ZimengXiong/ScrapNC/STLs/Z Assembly/M3 Spacer.stl

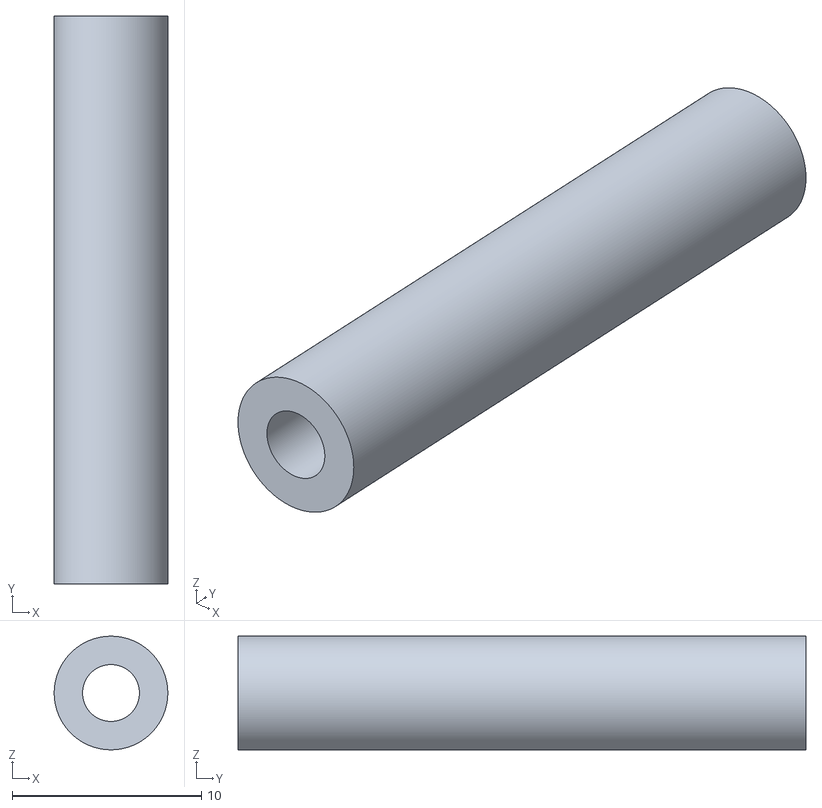
[picture p30: CAD file, 2025-07-05]
STLs/Z Assembly/M3 Spacer.stl
6.00 x 30.0 x 6.00
