ZimengXiong/ScrapNC/STLs/Electronics/Fly Pi Lite v2_DIN.stl

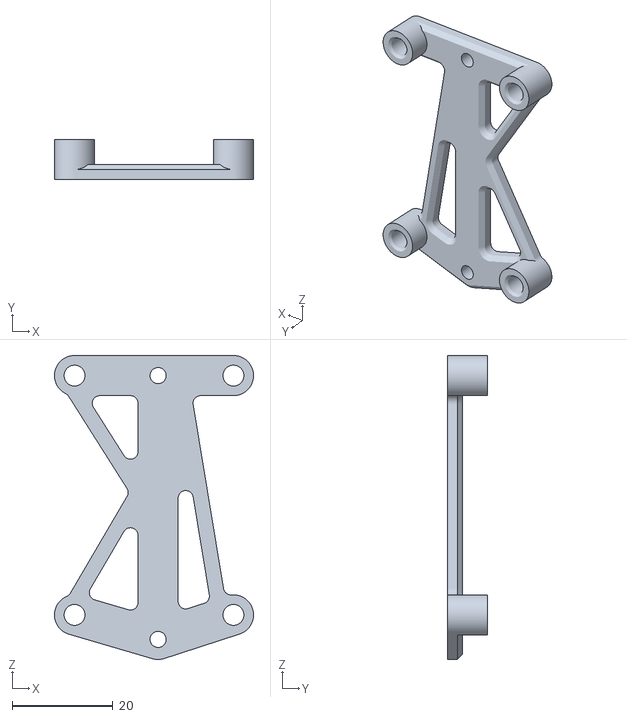
[picture p31: CAD file, 2025-07-05]
STLs/Electronics/Fly Pi Lite v2_DIN.stl
39.6 x 8.00 x 60.5
