ZimengXiong/ScrapNC/STLs/Y Axis Plate/Y Axis Plate Motor Mount.stl

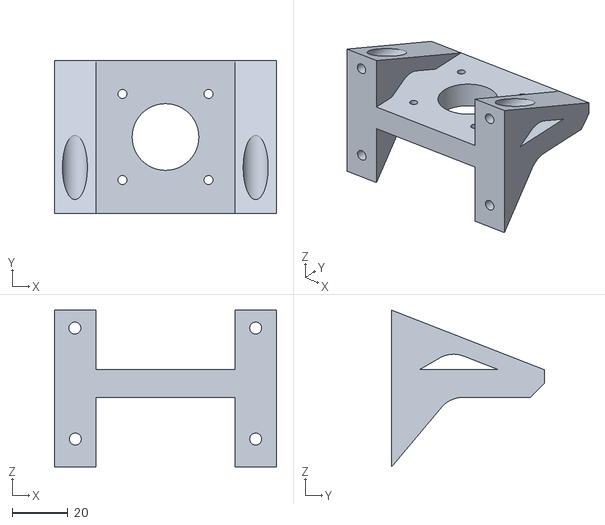
[picture p32: CAD file, 2025-07-05]
STLs/Y Axis Plate/Y Axis Plate Motor Mount.stl
80.0 x 55.0 x 56.4
