ZimengXiong/ScrapNC/STLs/Y Axis/Back Idler Mount Top.stl

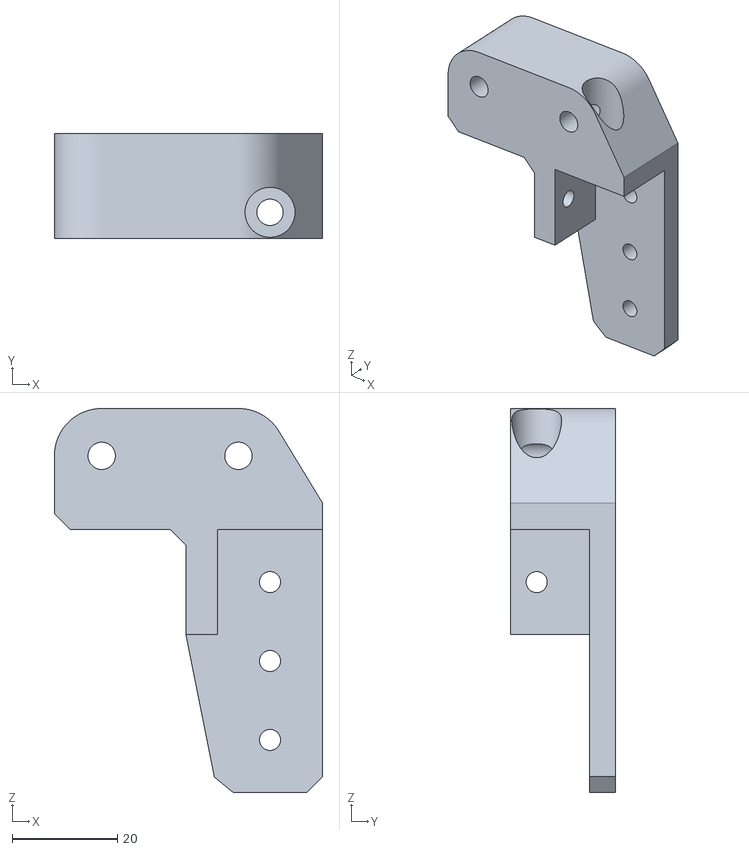
[picture p33: CAD file, 2025-07-05]
STLs/Y Axis/Back Idler Mount Top.stl
51.0 x 20.0 x 73.0
