ZimengXiong/ScrapNC/STLs/Y Axis Plate/Y Axis Belt Tensioner Module.stl

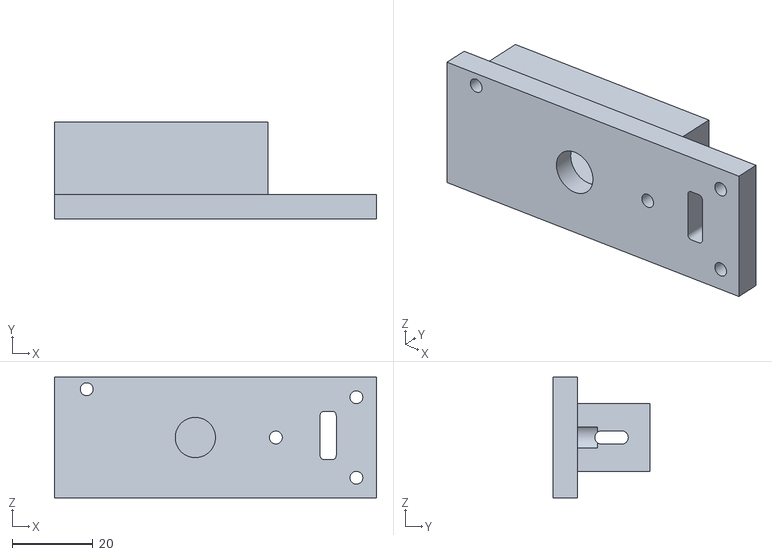
[picture p34: CAD file, 2025-07-05]
STLs/Y Axis Plate/Y Axis Belt Tensioner Module.stl
80.0 x 24.0 x 30.0
