ZimengXiong/ScrapNC/STLs/Y Axis/Back Idler Mount Bottom.stl

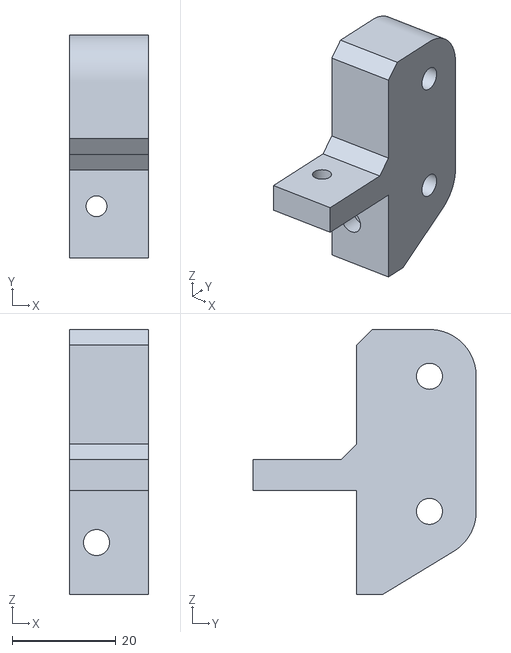
[picture p35: CAD file, 2025-07-05]
STLs/Y Axis/Back Idler Mount Bottom.stl
15.2 x 43.0 x 51.0
