ZimengXiong/ScrapNC/STLs/Y Axis Plate/Y Axis Plate Idler Tensioner Mount.stl

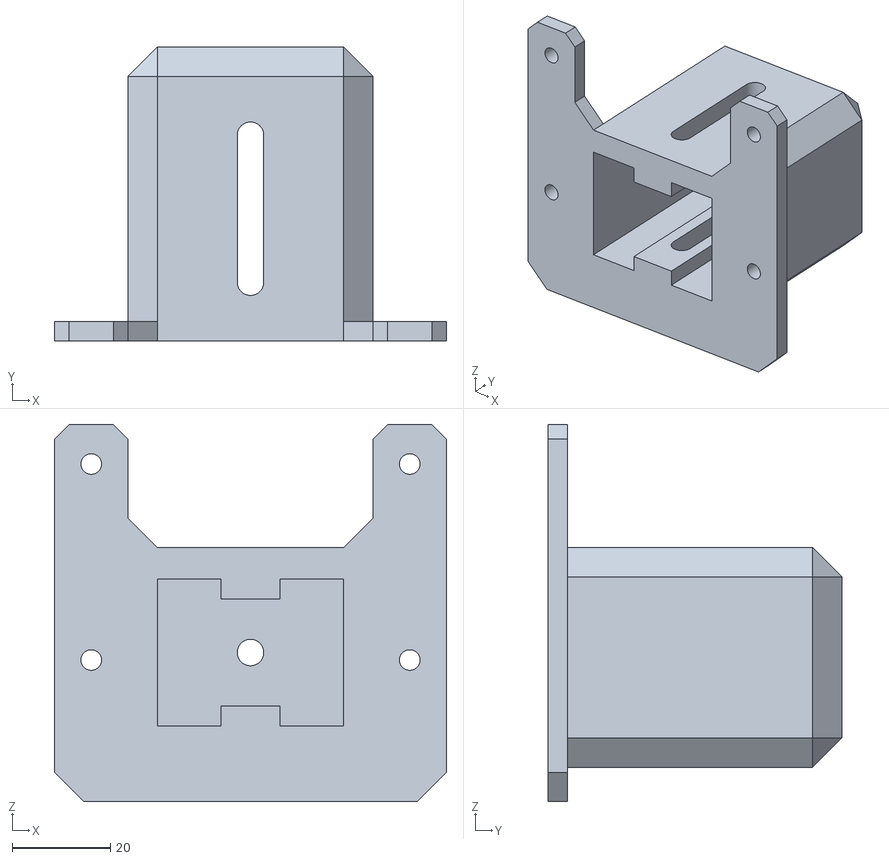
[picture p36: CAD file, 2025-07-05]
STLs/Y Axis Plate/Y Axis Plate Idler Tensioner Mount.stl
80.0 x 60.0 x 77.0
