ZimengXiong/ScrapNC/STLs/Y Axis/Y Axis Motor Mount Support.stl

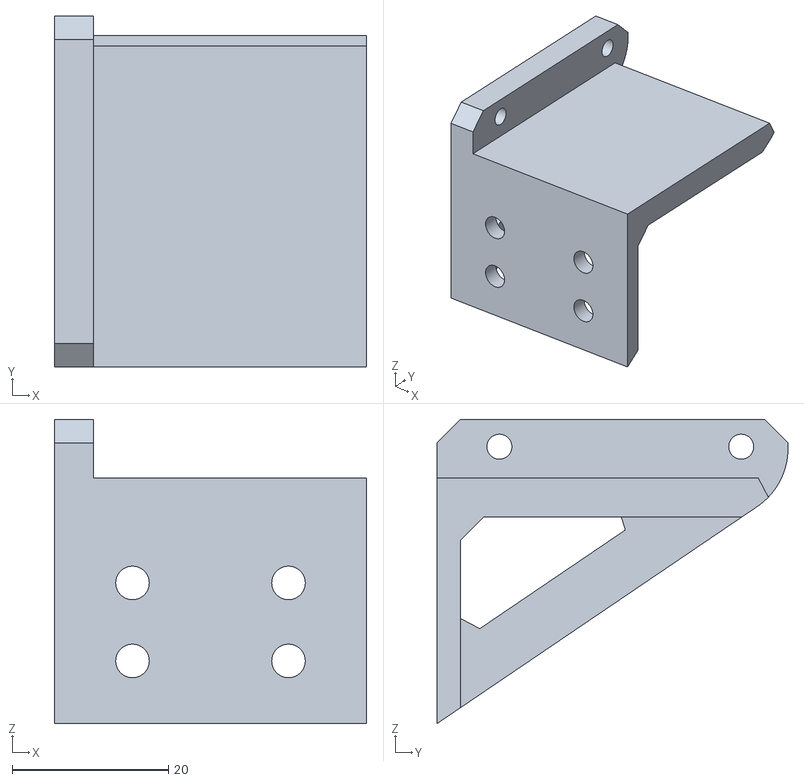
[picture p37: CAD file, 2025-07-05]
STLs/Y Axis/Y Axis Motor Mount Support.stl
40.0 x 45.0 x 39.0
