ZimengXiong/ScrapNC/STLs/Y Axis/Y Axis Front Idler Mount.stl

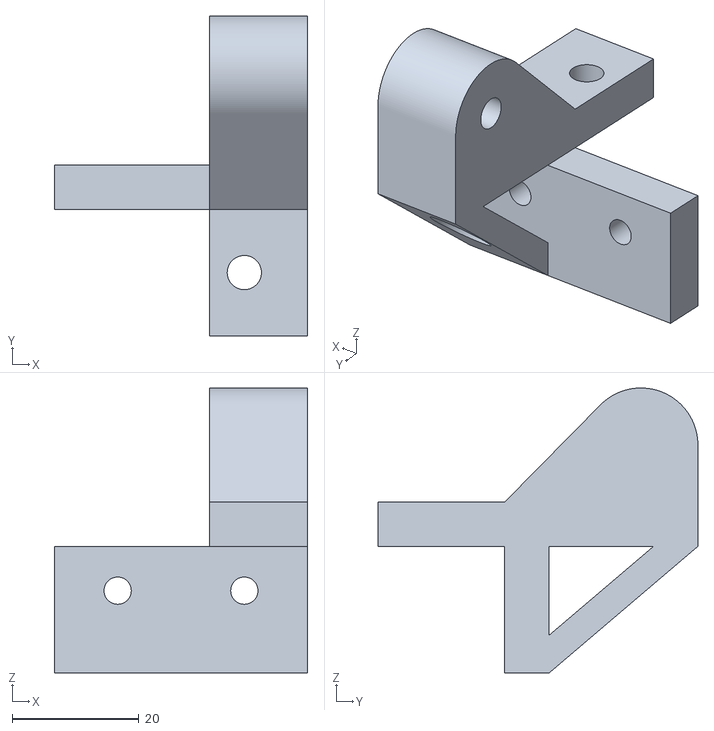
[picture p38: CAD file, 2025-07-05]
STLs/Y Axis/Y Axis Front Idler Mount.stl
40.0 x 50.5 x 45.0
