ZimengXiong/ScrapNC/STLs/Y Axis/Y Axis Endstop Mount.stl

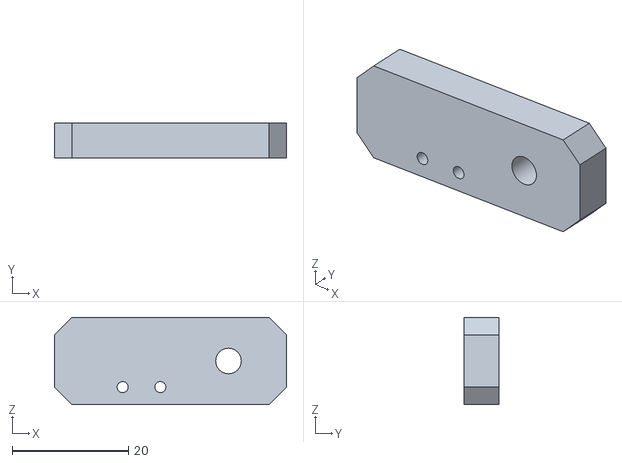
[picture p39: CAD file, 2025-07-05]
STLs/Y Axis/Y Axis Endstop Mount.stl
40.0 x 6.00 x 15.0
